ashpande/ProstheticHand/CAD Data/Final Model/Middle Finger Distal.SLDPRT

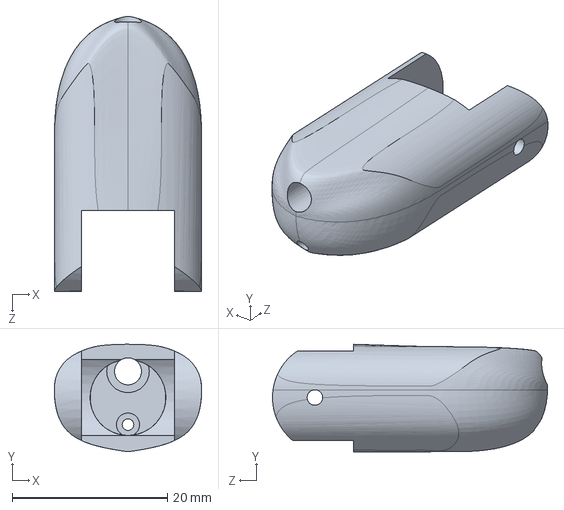
[picture p54: CAD file, 2020-03-19]
CAD Data/Final Model/Middle Finger Distal.SLDPRT
19.0 x 13.9 x 35.5 mm
