ashpande/ProstheticHand/CAD Data/Final Model/Ring Finger Bottom Proximal.SLDPRT

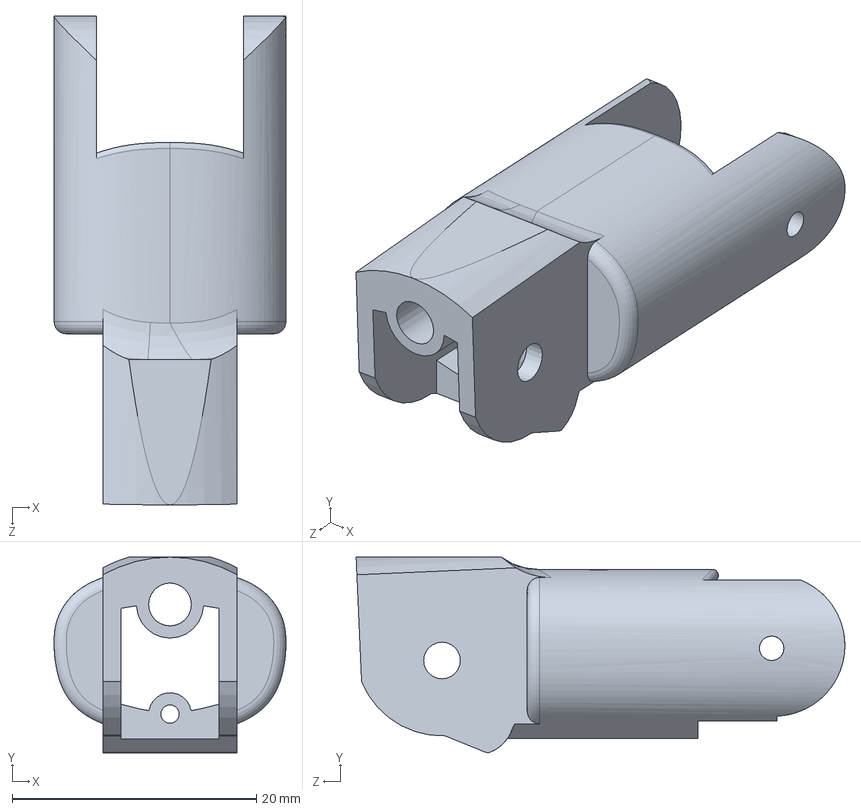
[picture p55: CAD file, 2020-03-19]
CAD Data/Final Model/Ring Finger Bottom Proximal.SLDPRT
19.0 x 16.0 x 40.0 mm
