ashpande/ProstheticHand/CAD Data/Final Model/Servo Horn.SLDPRT

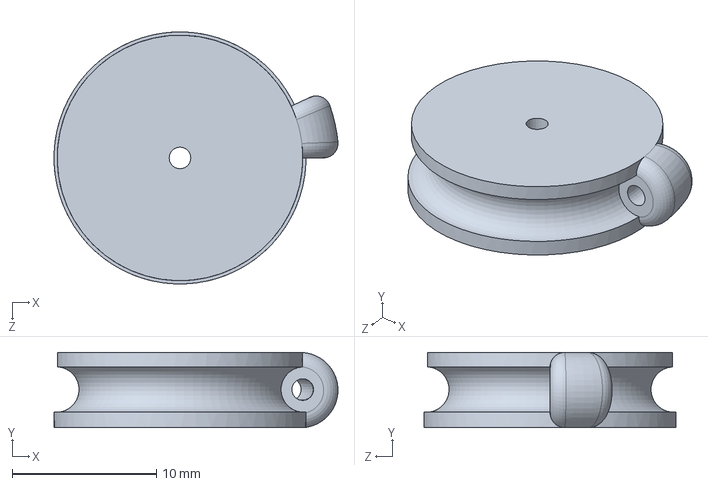
[picture p56: CAD file, 2020-03-19]
CAD Data/Final Model/Servo Horn.SLDPRT
19.7 x 5.20 x 17.5 mm
