ashpande/ProstheticHand/CAD Data/Final Model/Forearm1.SLDPRT

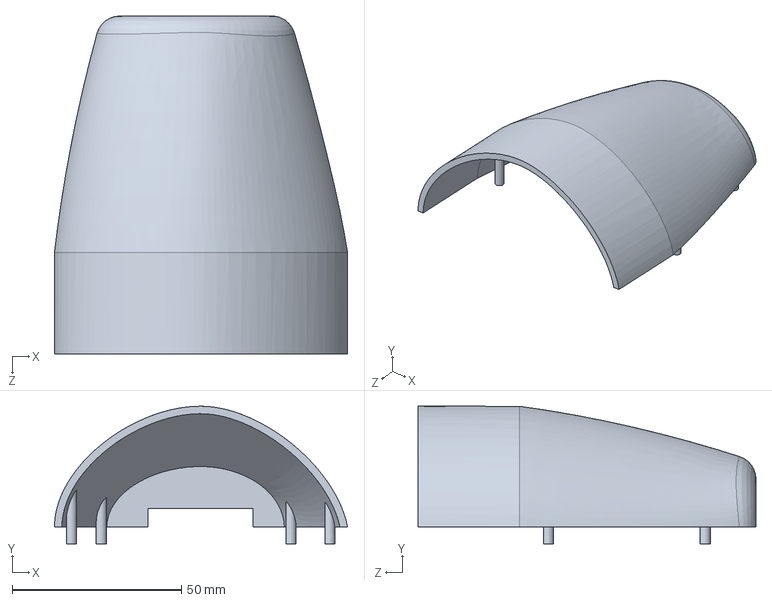
[picture p57: CAD file, 2020-03-19]
CAD Data/Final Model/Forearm1.SLDPRT
86.6 x 40.7 x 99.8 mm
