ashpande/ProstheticHand/CAD Data/Final Model/Thumb Middle.SLDPRT

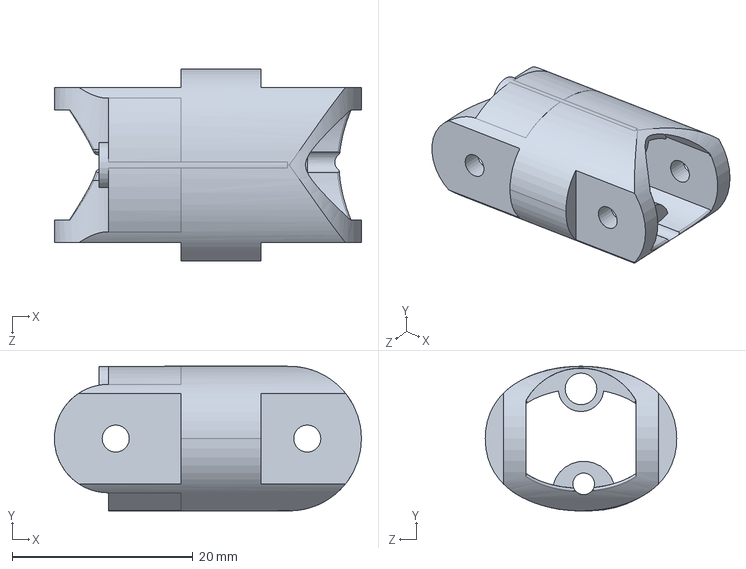
[picture p58: CAD file, 2020-03-19]
CAD Data/Final Model/Thumb Middle.SLDPRT
34.0 x 16.0 x 21.2 mm
