ashpande/ProstheticHand/CAD Data/Final Model/Thumb Lower.SLDPRT

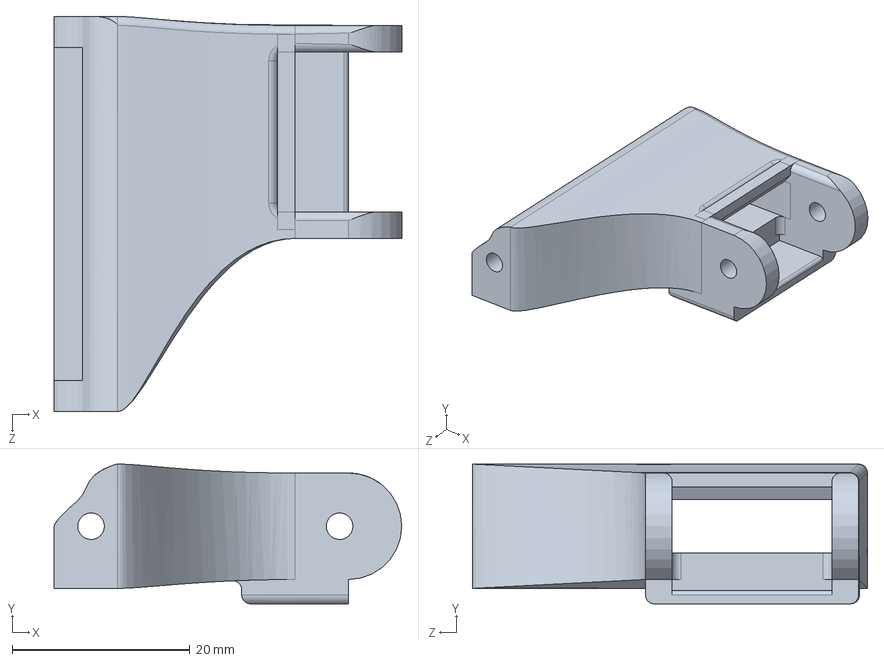
[picture p59: CAD file, 2020-03-19]
CAD Data/Final Model/Thumb Lower.SLDPRT
39.1 x 15.8 x 44.5 mm
