ashpande/ProstheticHand/CAD Data/Final Model/Forearm2.SLDPRT

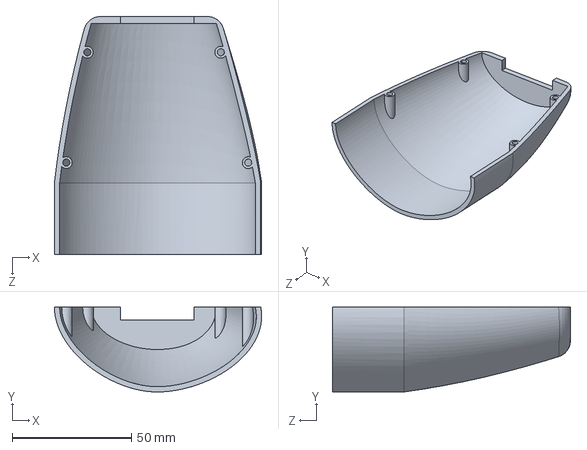
[picture p60: CAD file, 2020-03-19]
CAD Data/Final Model/Forearm2.SLDPRT
87.0 x 35.7 x 99.8 mm
